lwoodbury/audioNodes/circuits/powerManager/stripboard files/onOff button and powerboost.png

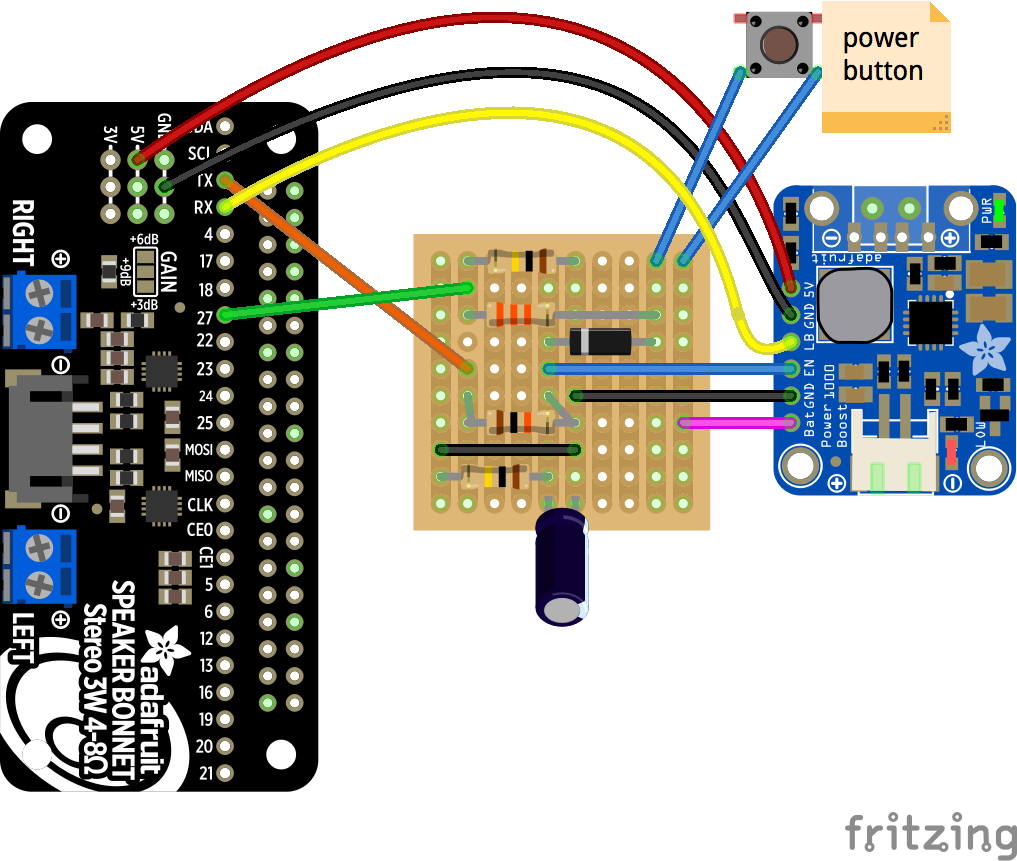
circuits/powerManager/stripboard files/onOff button and powerboost.png
