lwoodbury/audioNodes/circuits/volume buttons.png

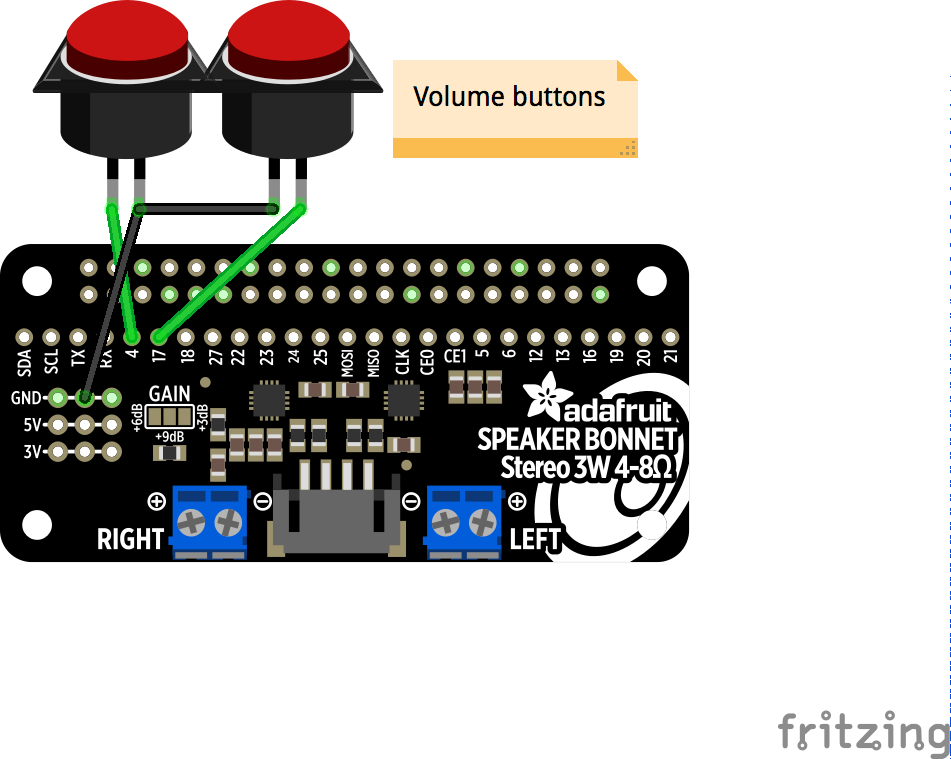
circuits/volume buttons.png
