lwoodbury/audioNodes/case designs/case layer order.png

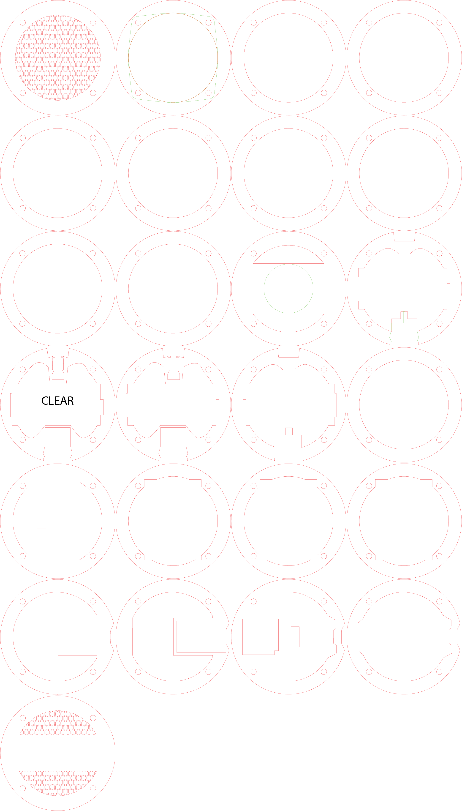
case designs/case layer order.png
