lwoodbury/audioNodes/build stage photos/IMG_1543.jpg

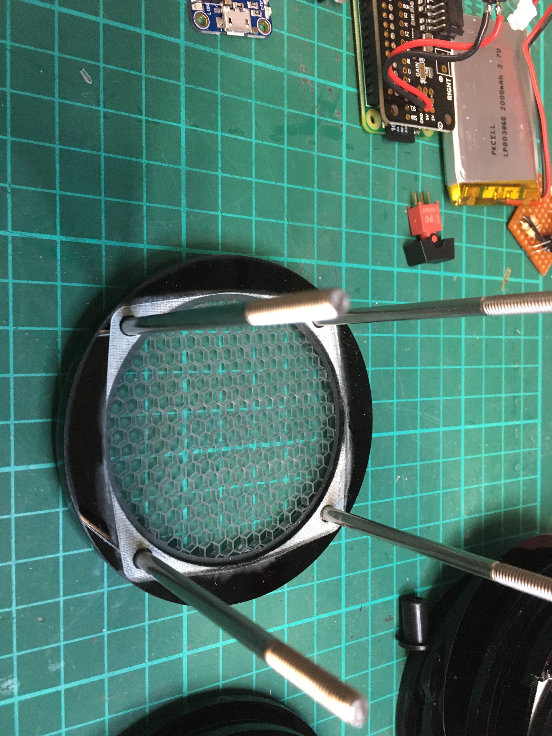
build stage photos/IMG_1543.jpg
