lwoodbury/audioNodes/build stage photos/IMG_1544.jpg

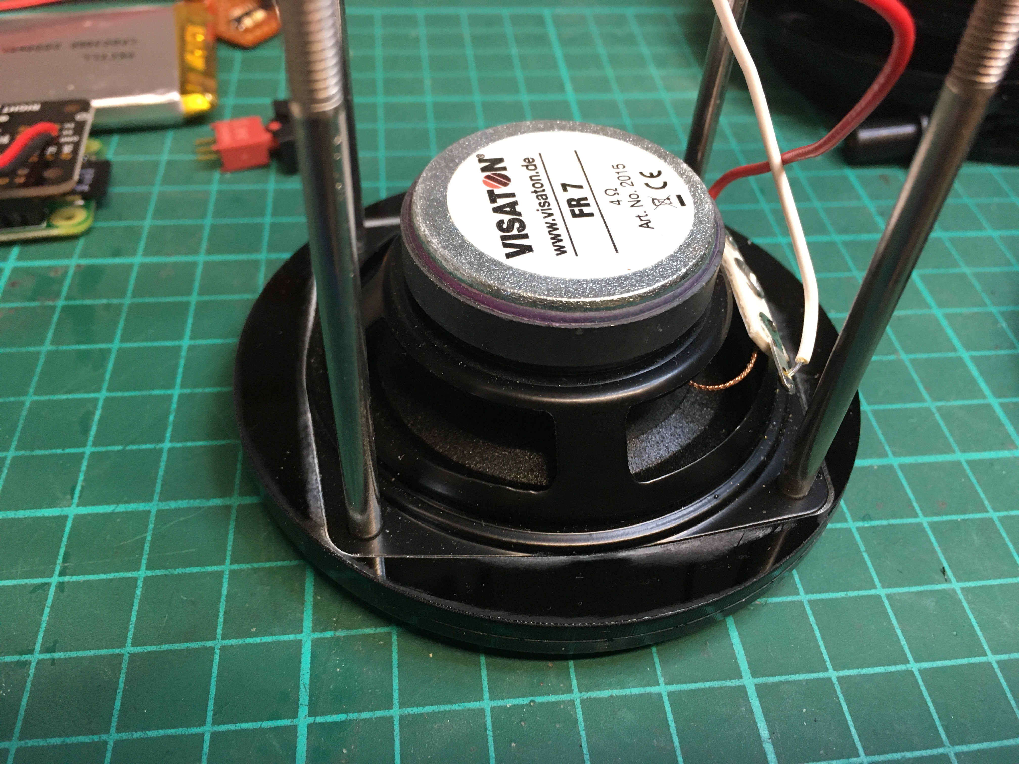
build stage photos/IMG_1544.jpg
