lwoodbury/audioNodes/build stage photos/IMG_1545.jpg

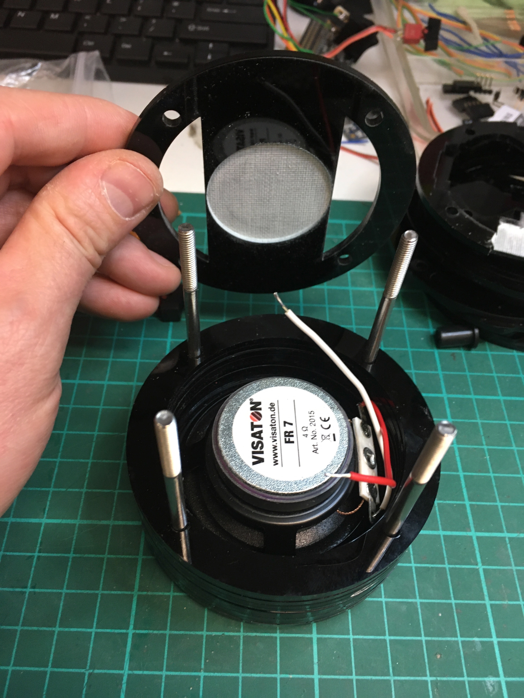
build stage photos/IMG_1545.jpg
