lwoodbury/audioNodes/build stage photos/IMG_1546.jpg

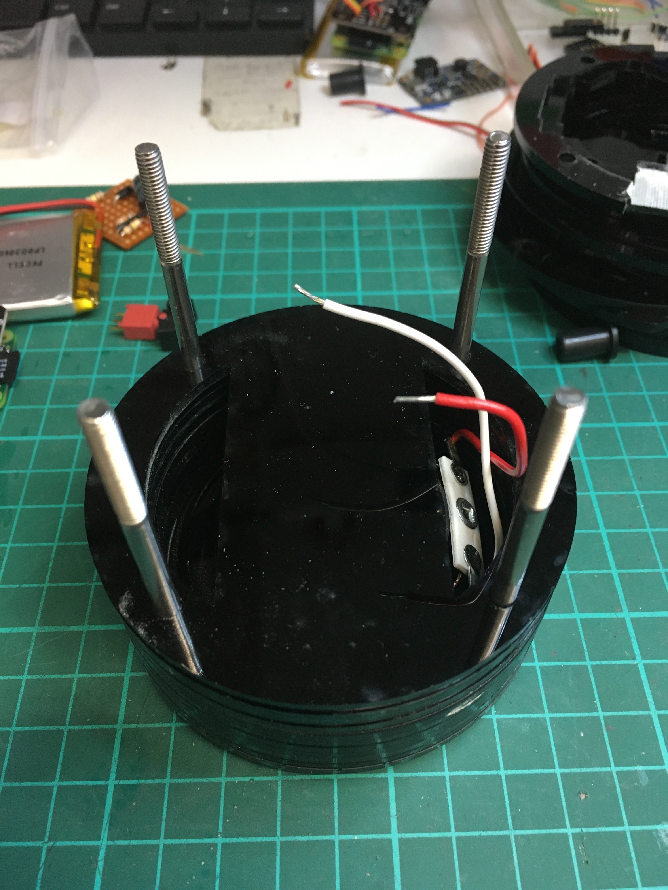
build stage photos/IMG_1546.jpg
