lwoodbury/audioNodes/build stage photos/IMG_1548.jpg

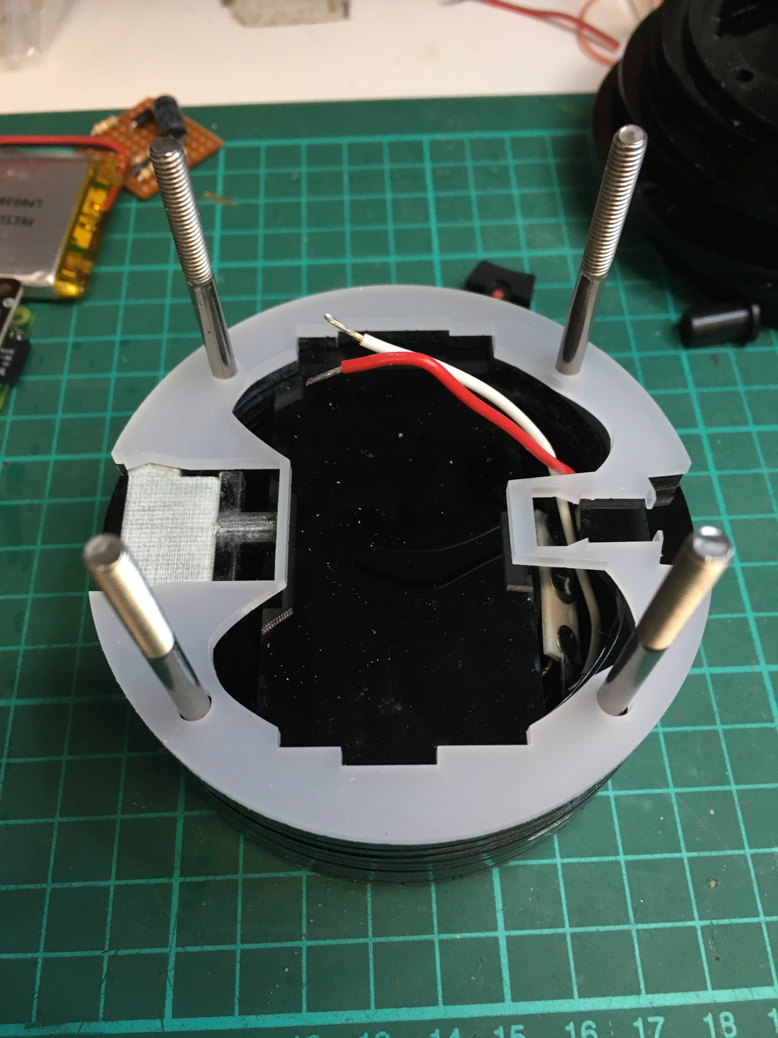
build stage photos/IMG_1548.jpg
