lwoodbury/audioNodes/build stage photos/IMG_1549.jpg

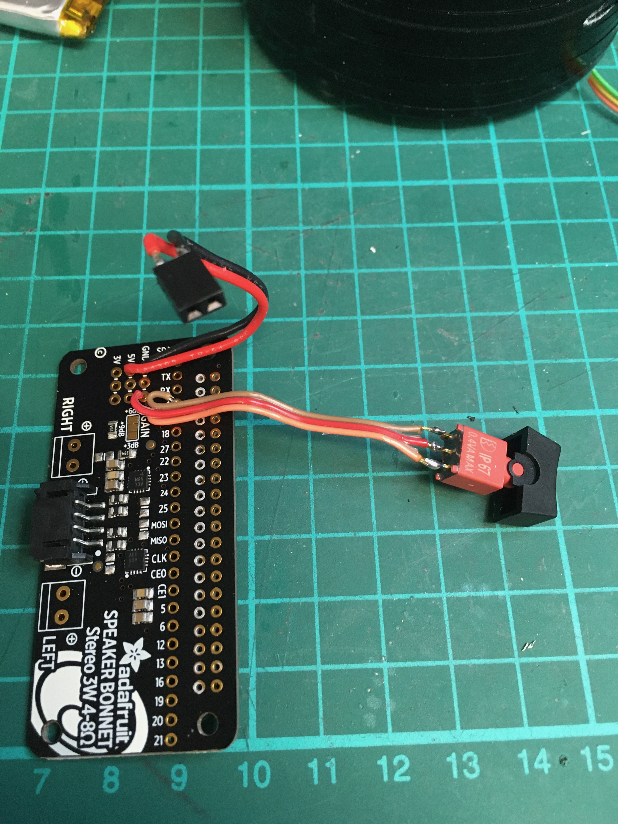
build stage photos/IMG_1549.jpg
