lwoodbury/audioNodes/build stage photos/IMG_1550.jpg

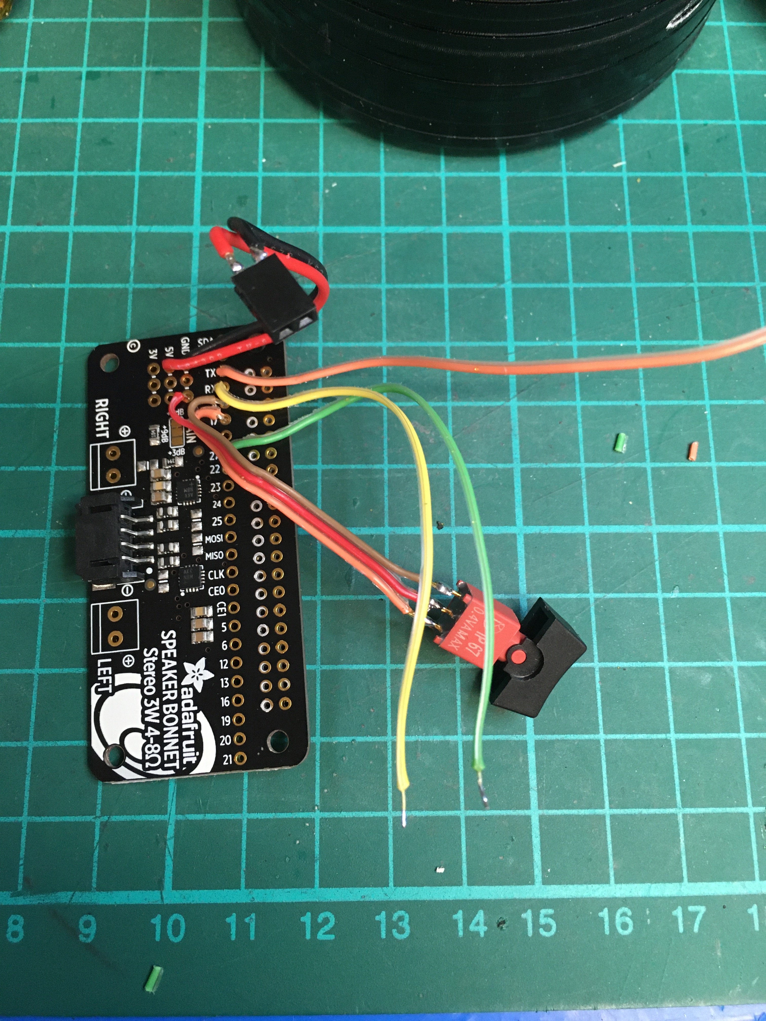
build stage photos/IMG_1550.jpg
