lwoodbury/audioNodes/build stage photos/IMG_1551.jpg

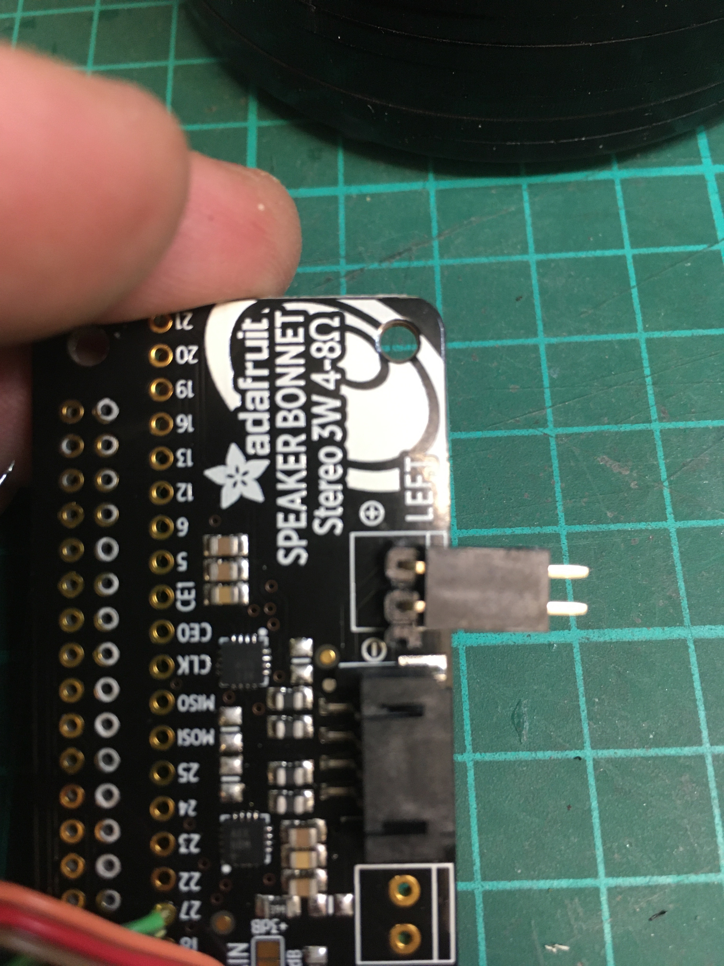
build stage photos/IMG_1551.jpg
