lwoodbury/audioNodes/build stage photos/IMG_1553.jpg

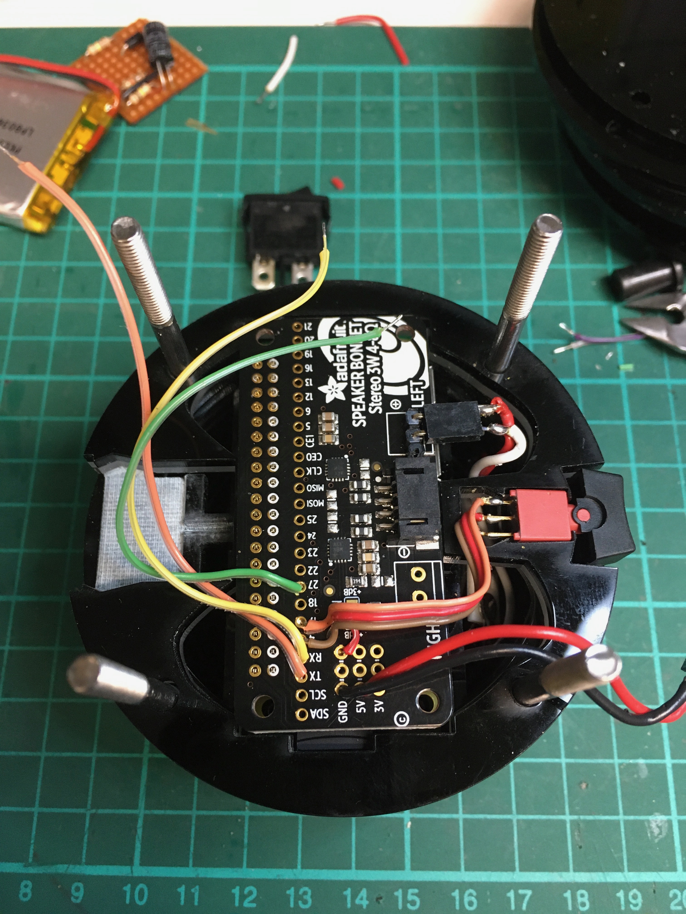
build stage photos/IMG_1553.jpg
