lwoodbury/audioNodes/build stage photos/IMG_1554.jpg

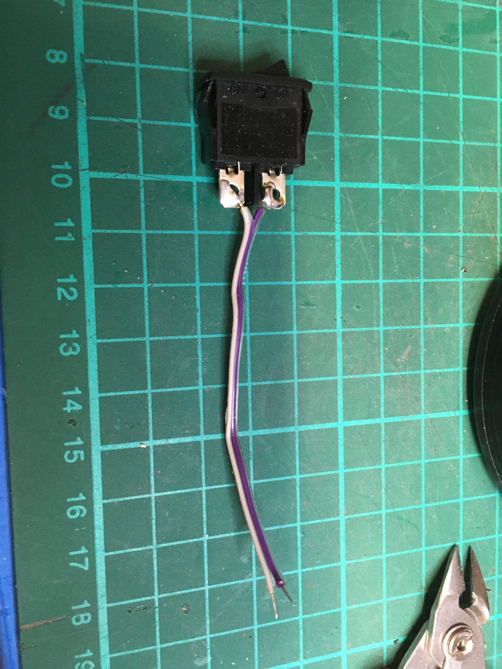
build stage photos/IMG_1554.jpg
