lwoodbury/audioNodes/build stage photos/IMG_1555.jpg

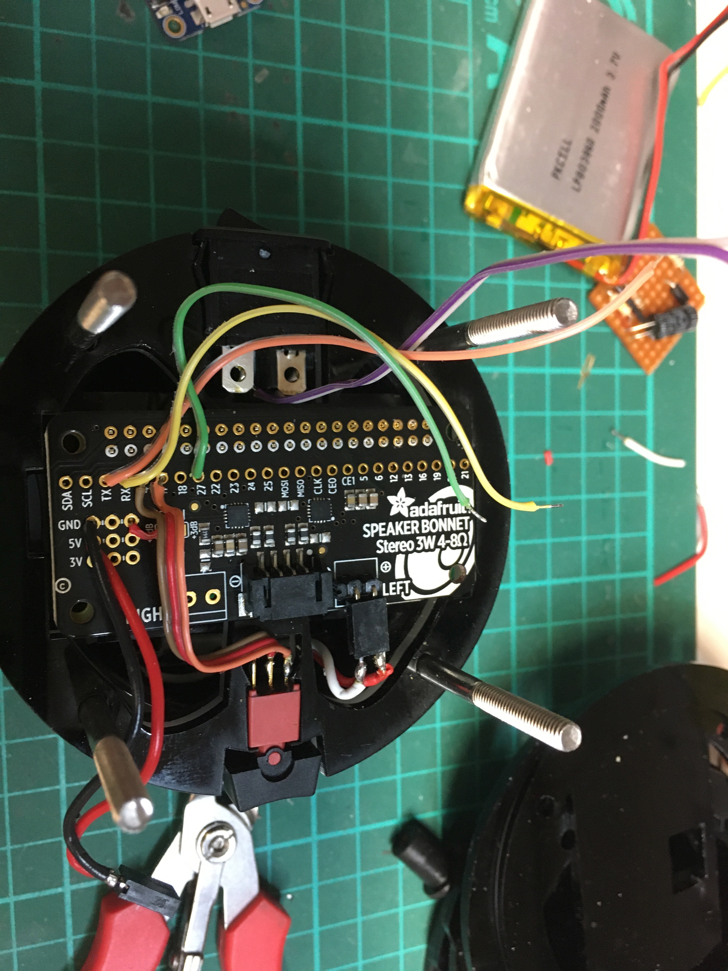
build stage photos/IMG_1555.jpg
