lwoodbury/audioNodes/build stage photos/IMG_1556.jpg

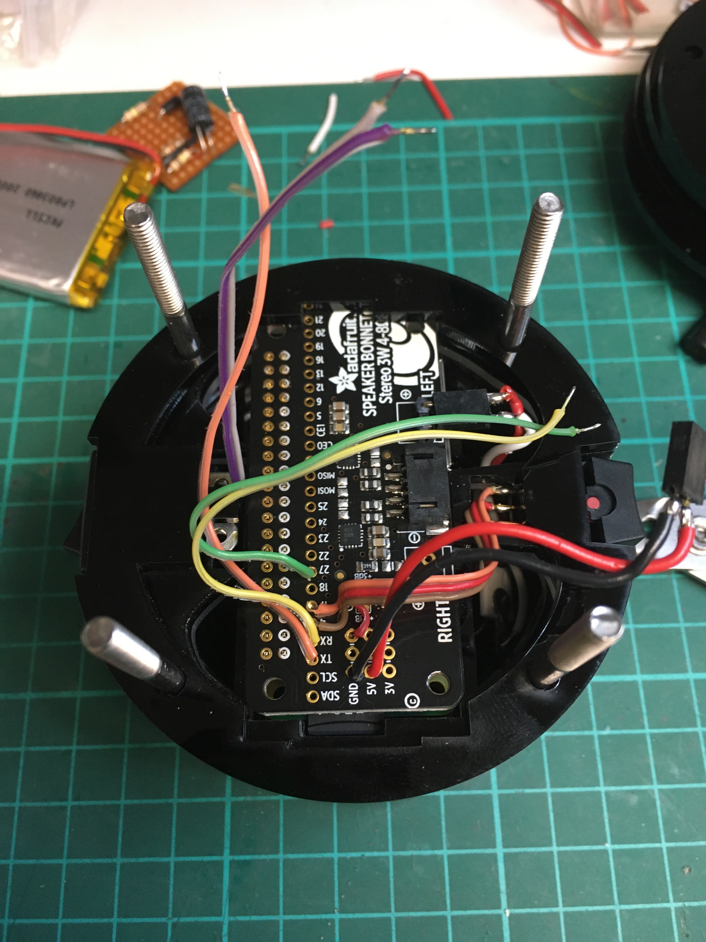
build stage photos/IMG_1556.jpg
