lwoodbury/audioNodes/build stage photos/IMG_1558.jpg

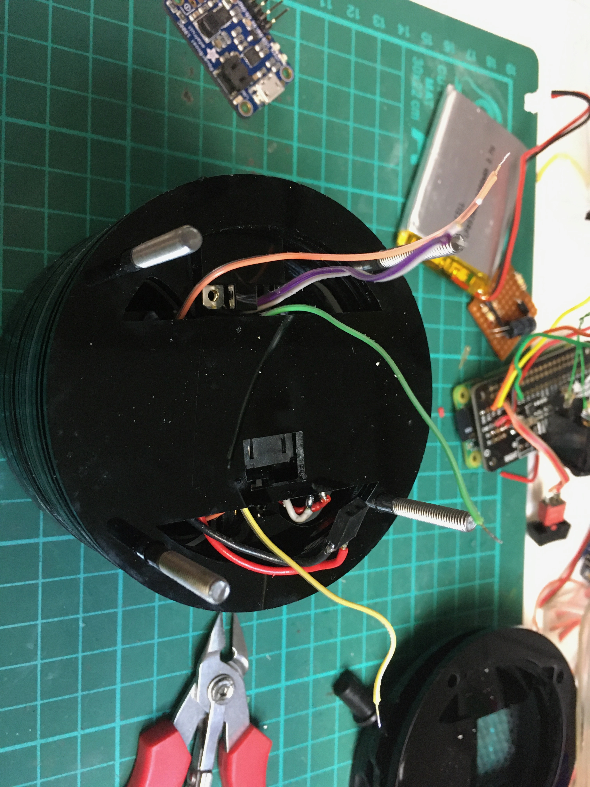
build stage photos/IMG_1558.jpg
