lwoodbury/audioNodes/build stage photos/IMG_1559.jpg

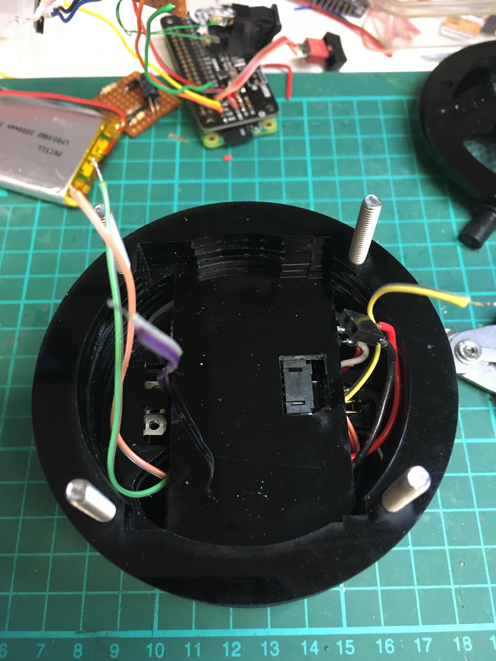
build stage photos/IMG_1559.jpg
