lwoodbury/audioNodes/build stage photos/IMG_1560.jpg

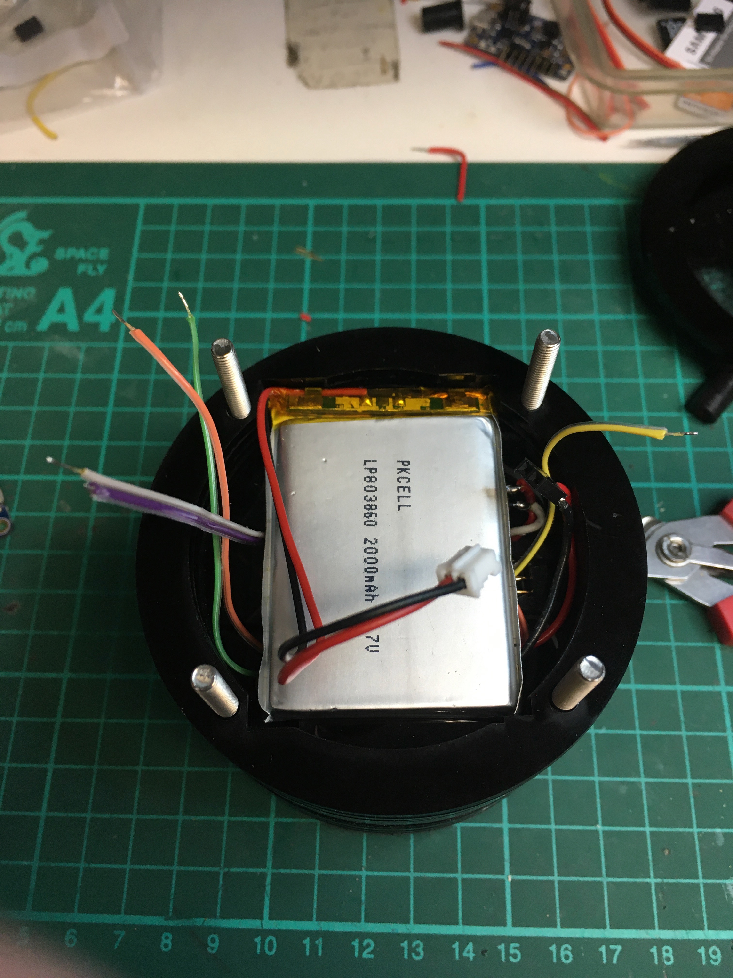
build stage photos/IMG_1560.jpg
