lwoodbury/audioNodes/build stage photos/IMG_1561.jpg

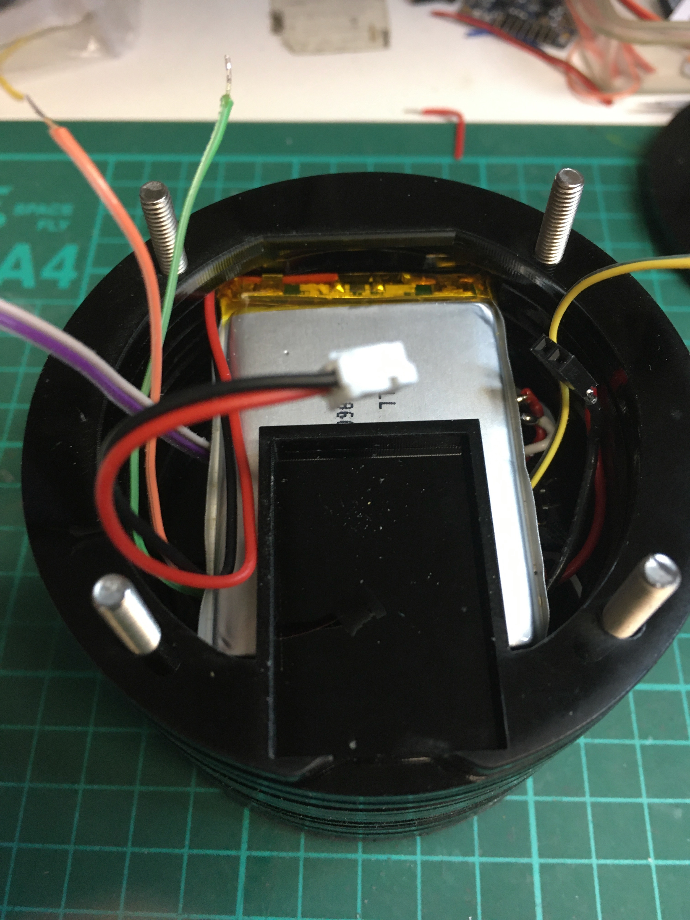
build stage photos/IMG_1561.jpg
