lwoodbury/audioNodes/build stage photos/IMG_1562.jpg

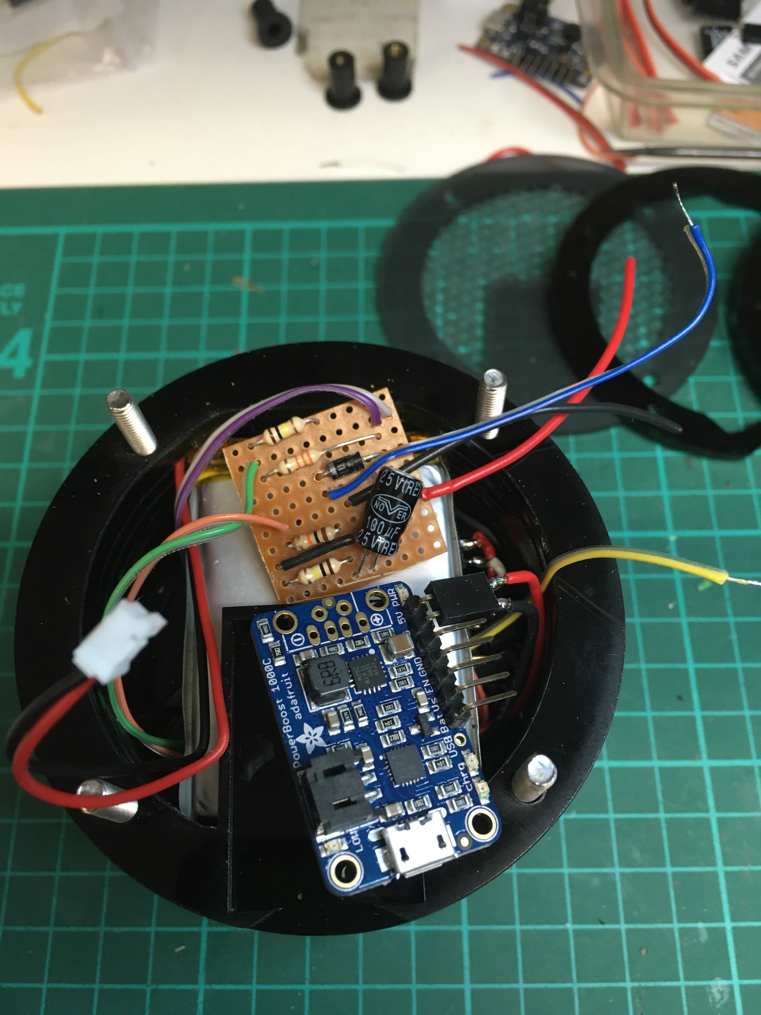
build stage photos/IMG_1562.jpg
