lwoodbury/audioNodes/build stage photos/IMG_1563.jpg

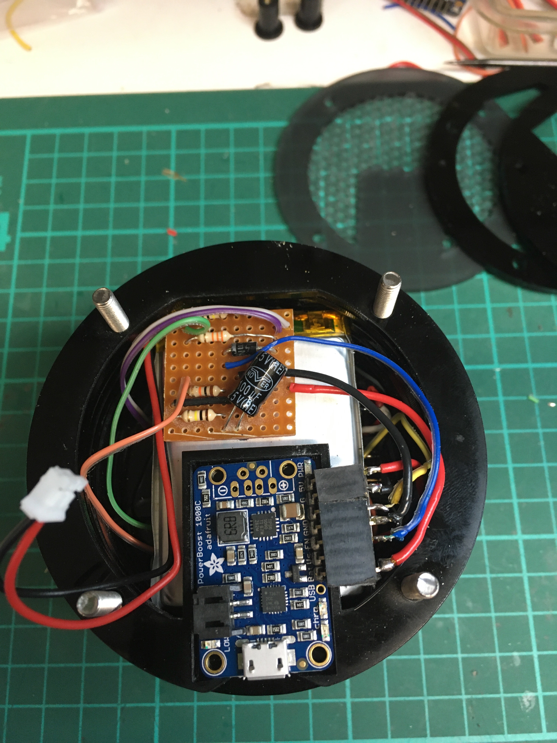
build stage photos/IMG_1563.jpg
