lwoodbury/audioNodes/build stage photos/IMG_1565.jpg

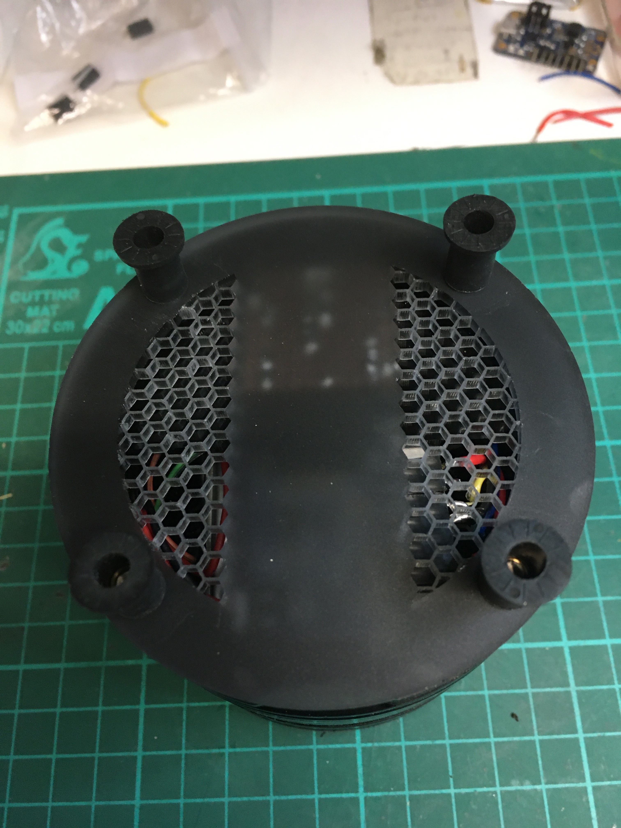
build stage photos/IMG_1565.jpg
