lwoodbury/audioNodes/build stage photos/IMG_1567.jpg

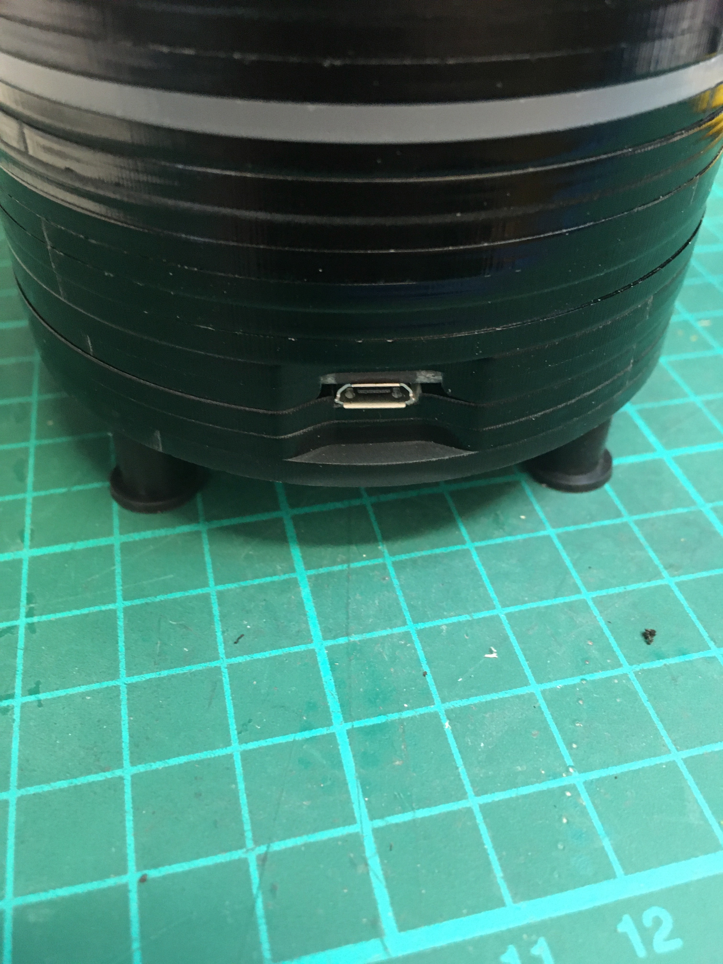
build stage photos/IMG_1567.jpg
